climatex/MegaFDC/MegaFDC/MegaFDC.ino

// MegaFDC (c) 2023-2025 J. Bogin, http://boginjr.com

// "Dummy" INO file to build from Arduino IDE
// For build and connection details see config.h and my website
// External libraries are in the "src" subdirectory
