climatex/MegaFDC/MegaFDC/fdc.h

// MegaFDC (c) 2023-2025 J. Bogin, http://boginjr.com
// Floppy disk controller interface
// Software compatible with a NEC uPD765 or any other PC FDC

#pragma once
#include "config.h"

// compile-time clock delay
#define DELAY_CYCLES(n) __builtin_avr_delay_cycles(n);
#define DELAY_MS(n)     DELAY_CYCLES(16000UL*n);

// FDC address registers
#define DCR 2 // drive control register (W only)
#define MSR 4 // main status register (R only)
#define DTR 5 // data register (R/W)
#define DRR 7 // data rate register (W) / disk change info, bit 0x80 (R)

// interrupt types
#define INTERRUPT_ACKNOWLEDGE 1 // acknowledge INT has been fired only
#define INTERRUPT_READ        2 // read data from disk
#define INTERRUPT_VERIFY      3 // read data from disk with no buffer storage
#define INTERRUPT_WRITE       4 // write data to disk

// special feature bit flags
#define SUPPORT_1MBPS         1 // supports CONFIGURE command to set up a FIFO buffer for 1 Mbps transfers (82077AA, PC8477)
#define SUPPORT_PERPENDICULAR 2 // supports PERPENDICULAR command for 2.88MB 3.5" support (82077AA, PC8477)

// inlined functions to query values from the FDC
inline BYTE readRegister(BYTE reg) __attribute__((always_inline));
inline void writeRegister(BYTE reg, BYTE value) __attribute__((always_inline));

// read 1 byte from chosen register
BYTE readRegister(BYTE reg)
{
  PORTC = (PORTC & 0xF8) | reg;   // set 3 bits of address lines
  DDRA = 0;                       // set data lines as input
  PORTC ^= 0x10;                  // toggle /RD
  DELAY_CYCLES(2);                // give it time to populate
  const BYTE value = PINA;        // read 8 bits of data lines
  PORTC ^= 0x10;                  // toggle /RD
   
  return value;
}

// write 1 byte to chosen register
void writeRegister(BYTE reg, BYTE value)
{ 
  PORTC = (PORTC & 0xF8) | reg;   // set 3 bits address lines
  DDRA = 0xFF;                    // set data lines as output
  PORTC ^= 0x20;                  // toggle /WR
  PORTA = value;                  // write 8 bits to data lines
  DELAY_CYCLES(2);                // delay two cycles
  PORTC ^= 0x20;                  // toggle /WR
}

class FDC
{
public:
  static FDC* get()
  {
    static FDC fdc;
    return &fdc;
  }
  
  // POD struct about disk, drive and logical media in it, 27 bytes
  struct DiskDriveMediaParams
  {
    BYTE DriveNumber;
    BYTE DriveInches;
    BYTE Cylinders;
    BYTE Heads;
    WORD SectorSizeBytes;
    BYTE SectorsPerTrack;
    BYTE GapLength;
    BYTE Gap3Length;
    BYTE LowLevelFormatFiller;
    BYTE SRT;
    WORD HLT;
    WORD HUT;    
    WORD CommRate;
    bool FM;
    bool DoubleStepping;
    bool DiskChangeLineSupport;
    bool PerpendicularRecording;
    bool UseFAT12;
    bool UseCPMFS;
    BYTE FATMediaDescriptor;
    BYTE FATRootDirEntries;
    WORD FATClusterSizeBytes;
  };
  
  // inquire status
  bool isIdle() { return m_idle; }
  bool isMotorOn() { return m_motorOn; }
  bool isDiskChanged();
  bool wasDiskChangeInquired() { return m_diskChangeInquired; }
  DiskDriveMediaParams* getParams() { return m_params; }
  BYTE getSpecialFeatures() { return m_specialFeatures; }
  
  // errors signaled when all retry attempts were exhausted; no disk/write protected: only 1 attempt
  bool getLastError() { return m_lastError; }
  bool wasErrorNoDiskInDrive() { return m_noDiskInDrive; }
  bool wasErrorDiskProtected() { return m_diskWriteProtected; }
  // read/write with DAM
  bool wasControlMark() { return m_controlMark; }
  // if true, print only fatal errors, no disk in drive or write protection
  void setSilentOnTrivialError(bool silent) { m_silentOnTrivialError = silent; }
  
  // CHS and sizes
  BYTE getCurrentCylinder() { return m_currentCylinder; }
  BYTE getCurrentHead() { return m_currentHead; }
  BYTE getCurrentSector() { return m_currentSector; }
  void convertLogicalSectorToCHS(WORD logicalSector, BYTE& cyl, BYTE& head, BYTE& sector);
  WORD getTotalSectorCount();
  BYTE getMaximumSectorCountForRW(BYTE startSector, WORD operationBytes = 0);
  BYTE convertSectorSize(WORD sectorSize);
  WORD getSectorSizeBytes(BYTE sectorSizeN);
  
  // floppy drive operations
  void motorOff();
  void resetController();
  void recalibrateDrive();
  void setCommunicationRate();
  void seekDrive(BYTE cylinder, BYTE head);
  bool readSectorID(BYTE* cyl = NULL, BYTE* head = NULL, BYTE* sector = NULL, BYTE* sectorSizeN = NULL);
  WORD readWriteSectors(bool writeOperation, BYTE startSector, BYTE endSector, WORD* dataPosition = NULL, bool deleted = false, BYTE* overrideCyl = NULL, BYTE* overrideHead = NULL);
  bool formatTrack(bool customCHSVTable = false, BYTE interleave = 1, BYTE startSector = 1);
  WORD verify(BYTE sector = 1, bool wholeTrack = true, BYTE* overrideCyl = NULL, BYTE* overrideHead = NULL);
  bool verifyTrack0(bool beforeWriteOperation = false);
  void setActiveDrive(DiskDriveMediaParams* newParams);
  void setAutomaticMotorOff(bool enabled = true);
  bool seekTest(BYTE toCylinder, BYTE step = 1);
  
private:  
  FDC();
  
  void motorOn(bool withDelay = true); // automatic
  void setInterrupt(BYTE operation = INTERRUPT_ACKNOWLEDGE);
  void waitForINT();
  bool waitForDATA();
  BYTE getData();
  void sendData(BYTE data);  
  void sendCommand(BYTE command);
  bool processIOResult(BYTE st0, BYTE st1, BYTE st2, BYTE endSectorNo);
  void fatalError(BYTE message);
  void setRecordingMode();
  BYTE* getInterleaveTable(BYTE sectorsPerTrack, BYTE interleave, BYTE startSector = 1);
  
  DiskDriveMediaParams* m_params;
  BYTE m_currentCylinder;
  BYTE m_currentHead;
  BYTE m_currentSector;
  bool m_idle;
  bool m_initialized;
  bool m_motorOn;
  bool m_noDiskInDrive;
  bool m_diskWriteProtected;
  bool m_diskChangeInquired;
  bool m_lastError;
  bool m_silentOnTrivialError;
  bool m_controlMark;
  
  BYTE m_specialFeatures;
};
